gastelumosiel/cetys-parking/firmware/STM32/mongoose/mongoose_fs.c

#include "mongoose.h"

#if defined(__cplusplus)
extern "C" {
#endif
const char *mg_unlist(size_t no);
const char *mg_unpack(const char *, size_t *, time_t *);
#if defined(__cplusplus)
}
#endif

static const unsigned char v1[] = {
  31, 139,   8,   0,   0,   0,   0,   0,   0,   3, 172, 125, // ...........}
 123, 119, 218, 198, 246, 232, 223, 247, 126,  10, 224, 248, // {w......~...
  82, 169,  12,  24, 176, 157, 135, 240, 152, 149,  58, 105, // R.........:i
 147,  54, 118, 122, 226,  56, 109,  67,  57,  94,   2,   6, // .6vz.8mC9^..
  80,  45,  75,  84,  18, 126, 196, 112,  63, 251, 221, 143, // P-KT.~.p?...
 153, 145,   4, 184, 237, 249, 173, 219, 149, 162, 209,  60, // ...........<
 247, 236, 215, 236, 189, 103,  70,  62, 174, 190, 254, 112, // .....gF>...p
 250, 233, 183, 159, 223,  84, 230, 217,  77, 120, 114, 124, // .....T..Mxr|
 163,  50, 191,  50, 158, 251,  73, 170,  50, 185, 204, 166, // .2.2..I.2...
 205,  23,  58,  47, 242, 111, 148, 188,  13, 212, 221,  34, // ..:/.o....."
  78, 178, 202,  56, 142,  50,  21, 101, 178, 118,  23,  76, // N..8.2.e.v.L
 178, 185, 156, 168, 219,  96, 172, 154, 244,  34,  42,  65, // .....`..."*A
  20, 100, 129,  31,  54, 211, 177,  31,  42, 217, 105, 181, // .d..6...*.i.
 107,  39, 199,  97,  16,  93,  87,  18,  21, 202,   0, 154, // k'.a.]W.....
  86, 230, 137, 154, 202,  48, 158, 197, 173, 244, 118,  86, // V....0....vV
 201,  30,  22,  74,   6,  55, 254,  76, 237, 195, 107, 227, // ...J.7.L..k.
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
 152, 131, 249, 190,  14,   7,  69, 212,  80, 122, 221,  11, // ......E.Pz..
  43, 247, 152,  74, 239, 135, 102, 102, 163,  57, 237,  94, // +..J..ff.9.^
  77, 156, 158,  51, 145, 183,  29,  40, 189, 118, 139, 233, // M..3...(.v..
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
